MyRetroStore/BBC-Master-ROM-Tester/software/Arduino/crc.h

struct t_crc_16k {
  char fileName[32];
  char hash[9];
};

static const t_crc_16k crc_16k[] PROGMEM = {
  {"Viewsheet B1.01", "078A9EE6"},
  {"MOS 3.50", "3D697D97"},
  {"DFS 2.45", "2C6370A"},
  {"Edit 1.50r", "F43EA8F7"},
  {"Basic 4r32","92327783"},
  {"DFS 2.0.5","27F1ADE0"},  
  {"View B3.3", "F6FB277D"},
  {"Terminal 1.20", "9693D8EC"},
  {"MOS 3.20", "90BBE4E6"},
  {"MOS 3.20", "2075CE7A"},
  {"DFS 2.24", "C8F2CAB4"},
  {"Viewsheet B1.0", "6AC1074F"},
  {"Basic", "7560D508"},
  {"Edit 1.00", "8EE994E1"},
  {"ADFS 1.5.0", "BA1F4164"},
  {"ADFS 1.33", "BE472EB5"},
  {"ADFS 1.30", "64EEC946"},
  {"ADFS 1.53", "58865F74"},
  {"ADFS 2.03", "4F867167"},
  {"View B3.0", "76007739"},
  {"Terminal 1.20", "F3A9F765"},
  {"MOS 2.00", "2D4C5C93"},
  {"MOS 2.00 Patched", "2742E8A"},
  {"MOS 1.20", "101DC533"},
  {"MOS 1.20 Patched", "20AA4793"},
  {"ARM 1.13", "70E3485B"},
  {"ARM 1.13", "9666402"},
  {"Exmon II 2.02", "947DB439"},
  {"Basic Editor 1.32", "A530B056"},
  {"View A3.0", "ADB2D1A6"},
  {"DFS 2.42", "CDD04F1C"},
  {"Basic", "B3E8F8E4"},
  {"ADT 2.00", "7BC4086F"},
  {"Toolkit Plus", "D35E75F3"},
  {"DumpMaster II 1.00", "37C3157B"},
  {"Snapper 1.20", "E1B32053"},
  {"View A3.0","C6DB4805"},
  {"DFS 2.26","E22CEA6F"},
  
}; // End of 16k marker
